Derkades/kart/dashboard/src/controller.h

#pragma once

#include <Arduino.h>
#include "config.h"
#include "params.h"

#define CONTROL_SERIAL_RECV_BUF_SIZE 64

class Controller {
    public:
        Controller(const char *name, uint32_t rx, uint32_t tx) : serial(rx, tx), name{name} {}

        const char *name;
        HardwareSerial serial;
        uint32_t lastWorking;
        int16_t feedbackSPD_AVG; // average motor speed RPM
        int16_t feedbackBATV; // battery voltage * 100
        int16_t feedbackDC_CURR; // total DC link current A * 100

        // Values must match default values in hoverboard controllers
        param pCtrlTyp = {false, P_CTRL_TYP, CTRL_TYP_SIN}; // COM, SIN, FOC
        param pCtrlMod = {false, P_CTRL_MOD, CTRL_MOD_VLT}; // VLT, SPD, TRQ
        param pIMotMax = {false, P_I_MOT_MAX, 15}; // Maximum motor current
        param pFiWeakEna = {false, P_FI_WEAK_ENA, 0}; // Field weakening / phase advance enabled
        param pFiWeakMax = {false, P_FI_WEAK_MAX, 2}; // Maximum field weakening current
        param pPhaAdvMax = {false, P_PHA_ADV_MAX, 30}; // Maximum phase advance angle
        param *params[5] = {&pCtrlTyp, &pIMotMax, &pFiWeakEna, &pFiWeakMax, &pPhaAdvMax};

        bool working() {
            return this->lastWorking && (this->lastWorking + CONTROL_SERIAL_WORKING_TIMEOUT_MS > millis());
        }

        void recv() {
            const uint32_t start = millis();
            char buf[CONTROL_SERIAL_RECV_BUF_SIZE];

            if (!this->serial.available()) {
                return;
            }

            // Read a line from serial
            size_t size = this->serial.readBytesUntil('\n', (uint8_t*) buf, CONTROL_SERIAL_RECV_BUF_SIZE);

            #ifdef CONTROL_SERIAL_RX_DEBUG_RAW
            Serial.print("RX ");
            Serial.print(controller.name);
            Serial.print("RAW ||");
            Serial.write(buf, size);
            Serial.println("||");
            #endif

            // Every line from the hoverboard should end with \r\n. We read up to \n, so the last character here should be \r.
            if (size < 1 || buf[size-1] != '\r') {
                #ifdef CONTROL_SERIAL_RX_DEBUG
                Serial.printf("RX %s ERR end\n", this->name);
                #endif
                return;
            }

            // Drop \r and add terminating null byte, so we can use str functions
            buf[size-1] = '\0';

            // We are receiving data, so controller is working
            this->lastWorking = millis();

            // Does this line contains a value reponse?
            if (strstr(buf, "# name:") == NULL) {
                #ifdef CONTROL_SERIAL_RX_DEBUG
                Serial.printf("RX %s ignore: %s\n", this->name, buf);
                #endif
                return;
            }

            char name[32];
            int16_t value;

            // Extract parameter name and value
            char *startQuote = strstr(buf, "\"");
            if (!startQuote) {
                #ifdef CONTROL_SERIAL_RX_DEBUG
                Serial.printf("RX %s ERR startQuote", this->name);
                #endif
                return;
            }

            char *endQuote = strstr(startQuote + 1, "\"");
            if (!endQuote) {
                #ifdef CONTROL_SERIAL_RX_DEBUG
                Serial.printf("RX %s ERR endQuote", this->name);
                #endif
                return;
            }

            memcpy(name, startQuote + 1, MIN(endQuote - startQuote - 1, 31));
            name[MIN(endQuote - startQuote - 1, 31)] = '\0';

            char *startValue = strstr(buf, "value:");
            if (!startValue) {
                #ifdef CONTROL_SERIAL_RX_DEBUG
                Serial.printf("RX %s ERR startValue", this->name);
                #endif
                return;
            }

            value = (int16_t) strtol(startValue + strlen("value:"), NULL, 10);

            #ifdef CONTROL_SERIAL_RX_DEBUG
            Serial.printf("RX %s name:%s val:%i\n", this->name, name, value);
            #endif

            this->processResponse(name, value);
        }

        void set(const char *param, const int16_t value) {
            char command[32];
            snprintf(command, 32, "$SET %s %i\n", param, value);
            this->sendCommand(command);
        }

        void get(const char *param) {
            char command[32];
            snprintf(command, 32, "$GET %s\n", param);
            this->sendCommand(command);
        }

    private:
        void processResponse(char *name, int16_t value) {
            // See if received name is a parameter

            for (param *p : this->params) {
                if (strcmp(p->name, name) == 0) {
                    if (p->value != value) {
                        #ifdef CONTROL_SERIAL_RX_DEBUG
                        Serial.printf("RX %s %s val %i not match %i\n", this->name, name, value, p->value);
                        #endif
                        return;
                    }

                    // Correct value is set, parameter is no longer dirty
                    p->dirty = false;

                    #ifdef CONTROL_SERIAL_RX_DEBUG
                    Serial.printf("RX %s %s OK dirty=>false\n", this->name, p->name);
                    #endif
                    return;
                }
            }

            // Otherwise maybe a variable
            if (strcmp(name, V_DC_CURR) == 0) {
                this->feedbackDC_CURR = value;
            } else if (strcmp(name, V_SPD_AVG) == 0) {
                this->feedbackSPD_AVG = value;
            } else if (strcmp(name, V_BATV) == 0) {
                this->feedbackBATV = value;
            } else {
                // Unknown name
                Serial.printf("RX %s unknown name: %s\n", this->name, name);
            }
        }

        void sendCommand(char *command) {
            #ifdef CONTROL_SERIAL_TX_DEBUG
            Serial.printf("TX %s: %s", this->name, command);
            #endif

            this->serial.write(command);
        }
};
